Recycling-Werkstatt-insel-eV/Nistkasten_4_Blumenkasten/Documentation/Anordnung_3D_Druck_Komponenten_transparent.jpg

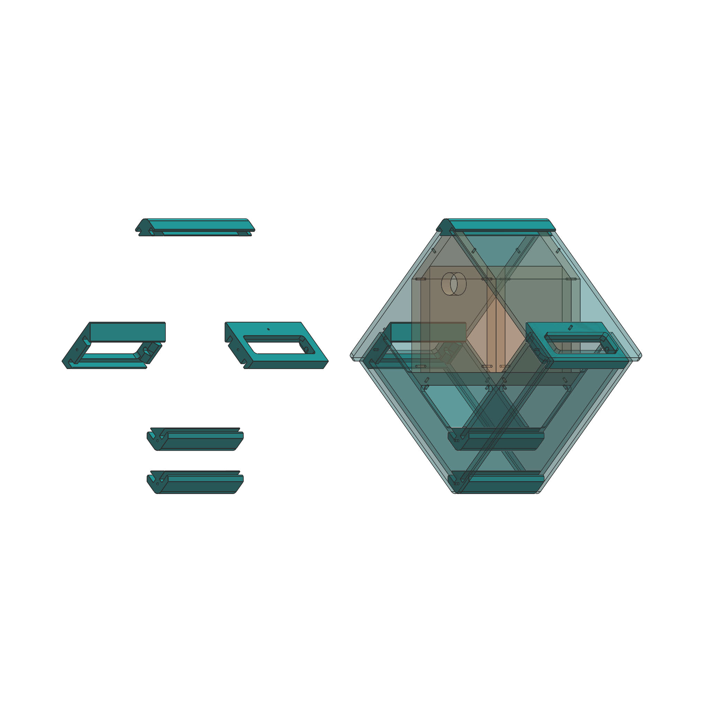
Documentation/Anordnung_3D_Druck_Komponenten_transparent.jpg
